stawiski/LAUNCHXL-F28027-isolation-PCB/photos/photo1.jpg

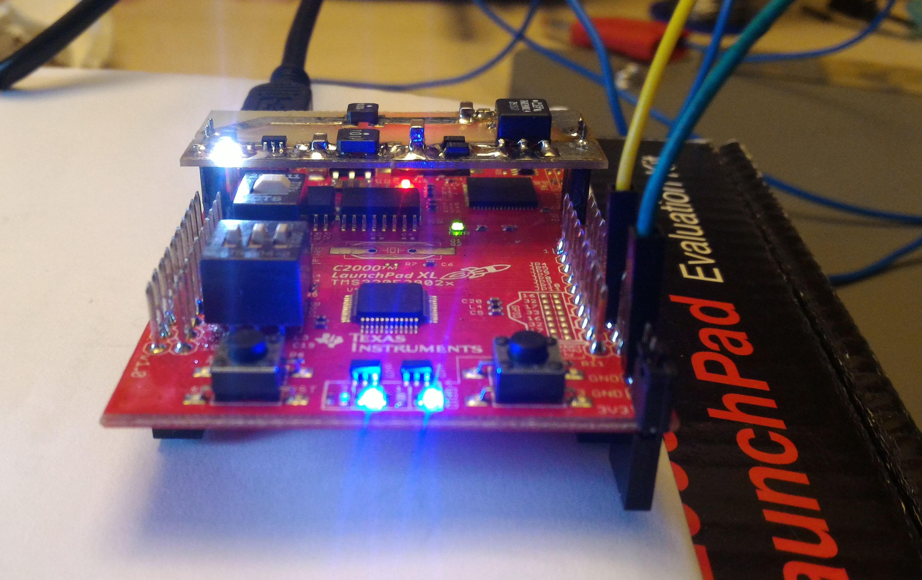
photos/photo1.jpg
