stawiski/LAUNCHXL-F28027-isolation-PCB/photos/photo2.jpg

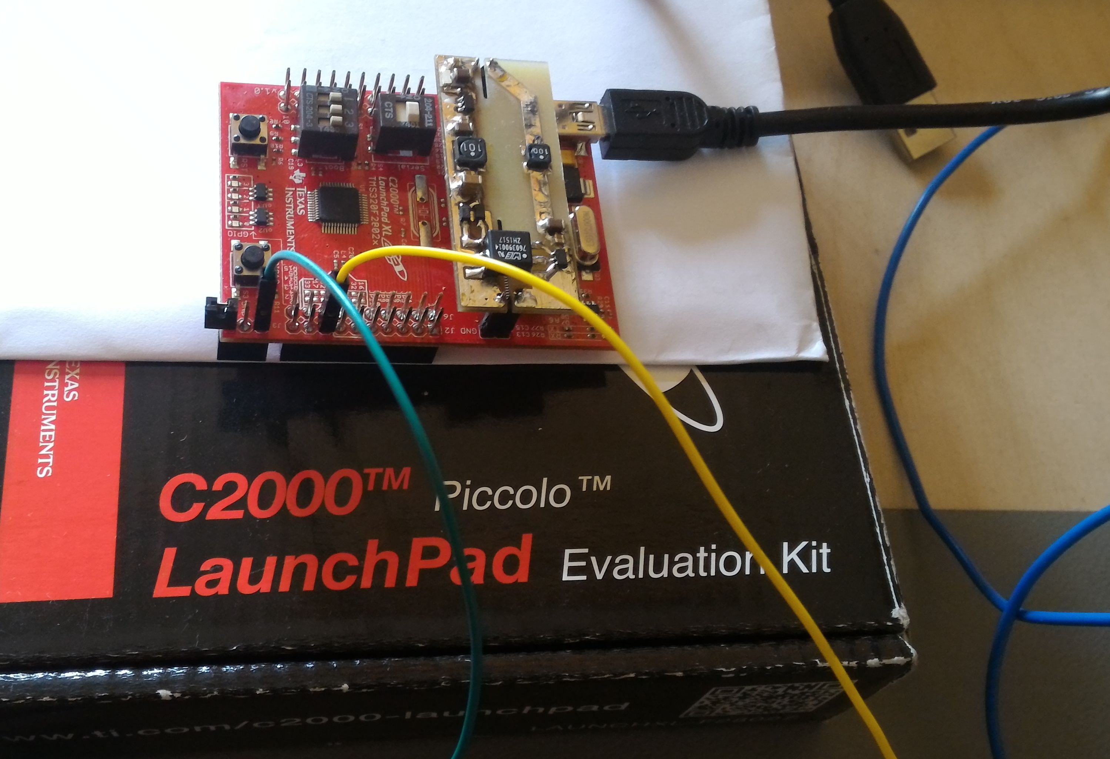
photos/photo2.jpg
